scostella/Arduino-Light-Controller/Arduino Light Controller.kicad_sch

## KiCad design Arduino Light Controller.kicad_sch (2026-01-30)

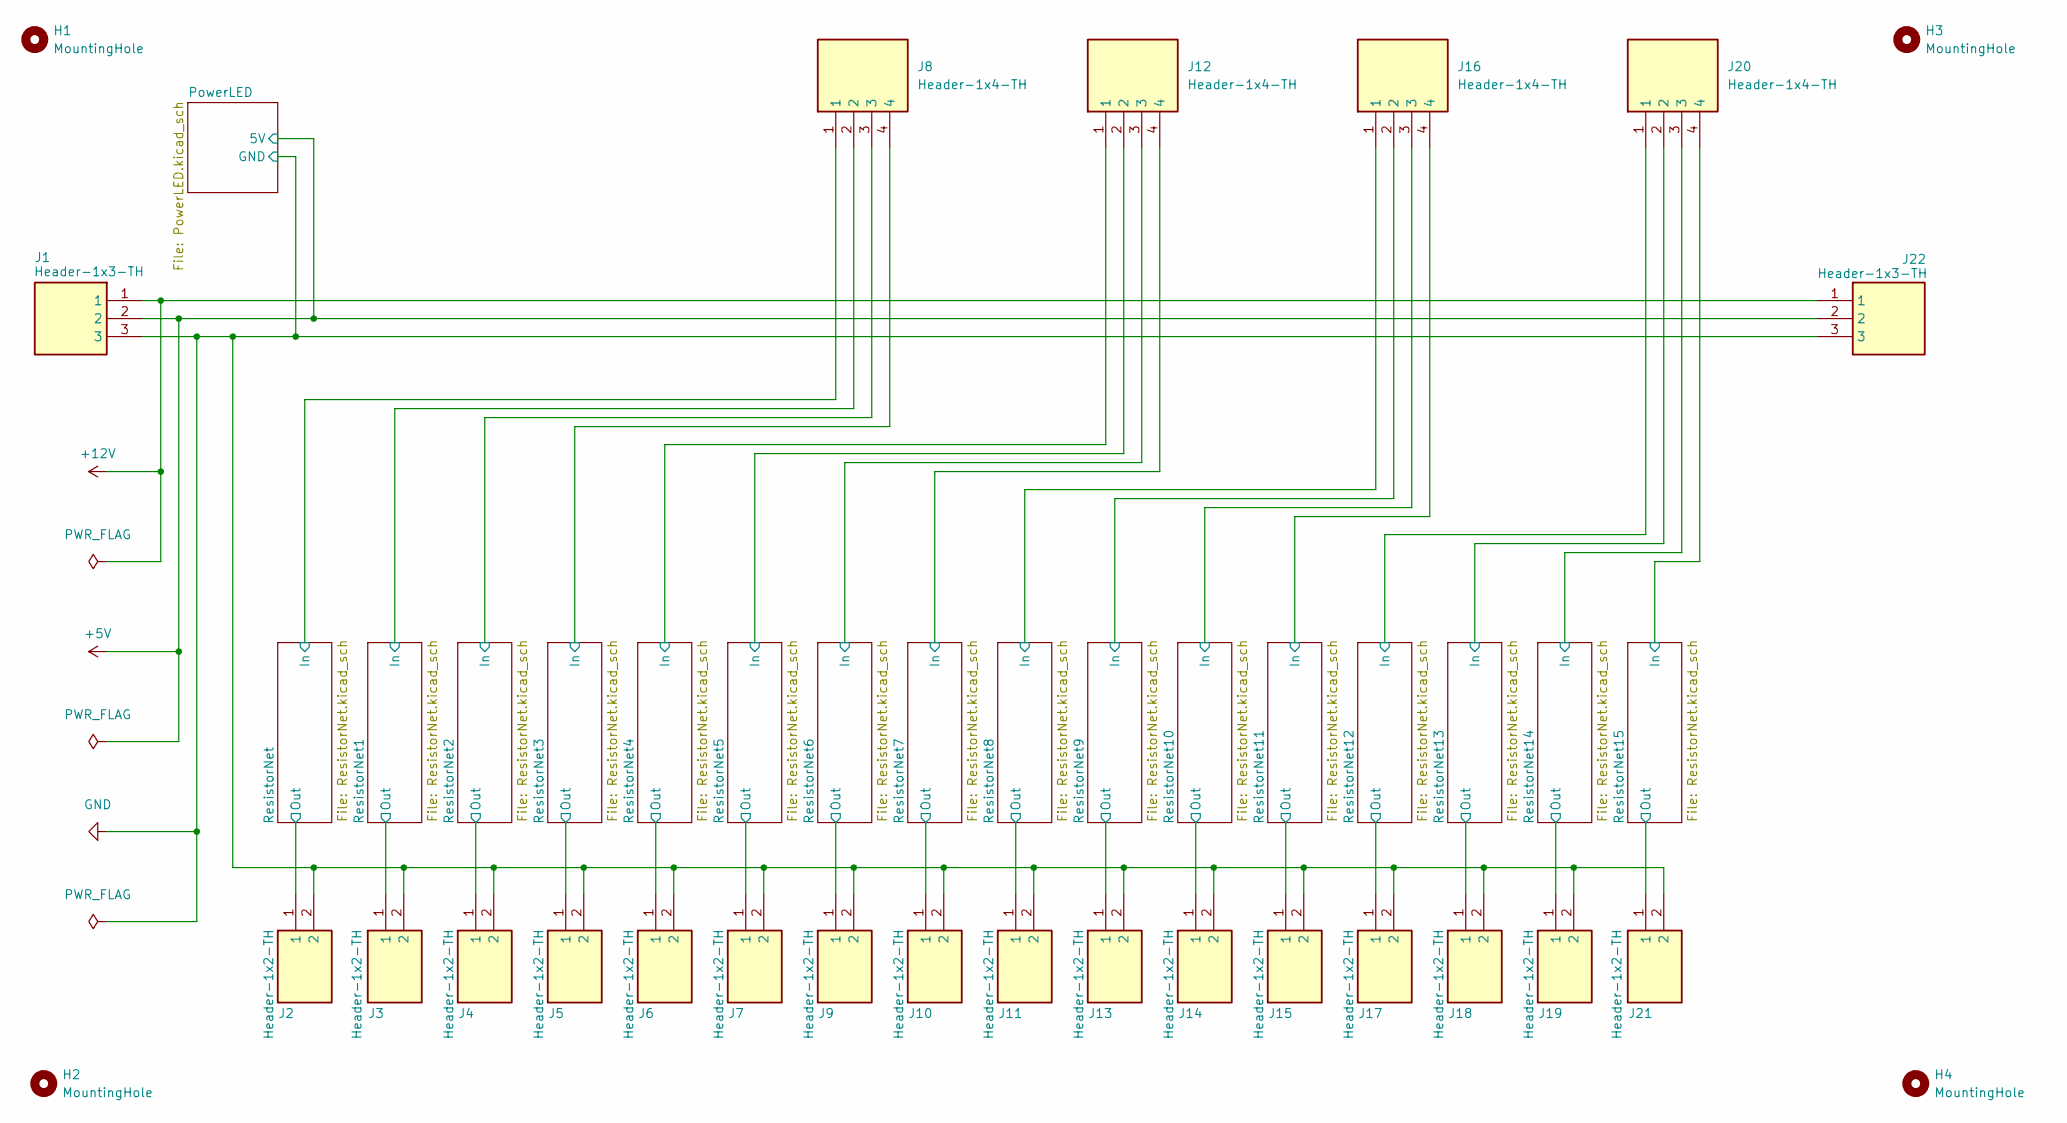
[picture p2: schematic Arduino Light Controller.kicad_sch]

Parts:
H1, H2, H3, H4: MountingHole; MountingHole_3.2mm_M3_ISO7380
J1, J22: Header-1x3-TH; 710-61300311121; Mouser Part Number 710-61300311121
J2, J3, J4, J5, J6, J7, J9, J10, J11, J13, J14, J15, J17, J18, J19, J21: Header-1x2-TH; 710-61300211121; Mouser Part Number 710-61300211121
J8, J12, J16, J20: Header-1x4-TH; 710-61300411121; Mouser Part Number 710-61300411121

Connections:
+5V: J1.2, J22.2
+12V: J1.1, J22.1
GND: J1.3, J2.2, J3.2, J4.2, J5.2, J6.2, J7.2, J9.2, J10.2, J11.2, J13.2, J14.2, J15.2, J17.2, J18.2, J19.2, J21.2, J22.3
In: J8.1, J8.2, J8.3, J8.4, J12.1, J12.2, J12.3, J12.4, J16.1, J16.2, J16.3, J16.4, J20.1, J20.2, J20.3, J20.4
Out: J2.1, J3.1, J4.1, J5.1, J6.1, J7.1, J9.1, J10.1, J11.1, J13.1, J14.1, J15.1, J17.1, J18.1, J19.1, J21.1
