scostella/Arduino-Light-Controller/PowerLED.kicad_sch

## KiCad design PowerLED.kicad_sch (2026-01-31)

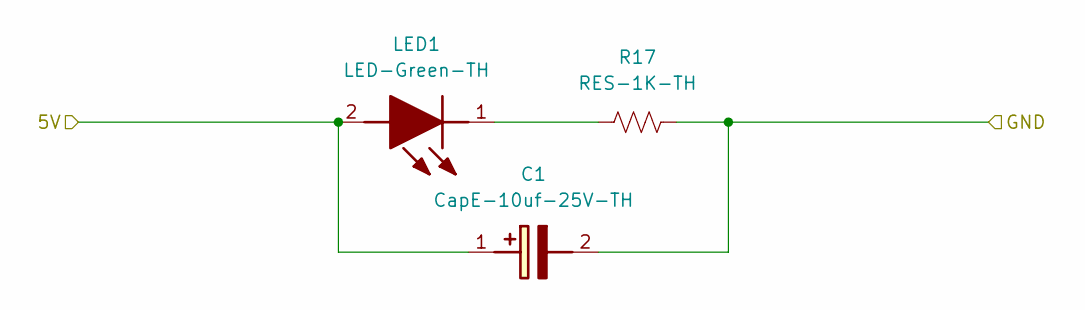
[picture p3: schematic PowerLED.kicad_sch]

Parts:
C1: CapE-10uf-25V-TH; 710-860010472002; Mouser Part Number 710-860010472002
LED1: LED-Green-TH; 604-WP7113GD; Mouser Part Number 604-WP7113GD
R17: RES-1K-TH; R_Axial_DIN0204_L3.6mm_D1.6mm_P7.62mm_Horizontal; Mouser Part Number N/A

Connections:
5V: C1.1 (+), LED1.2 (A)
GND: C1.2 (-), R17.2
unnamed: LED1.1 (K), R17.1
