scostella/Arduino-Light-Controller/ResistorNet.kicad_sch

## KiCad design ResistorNet.kicad_sch (2026-01-30)

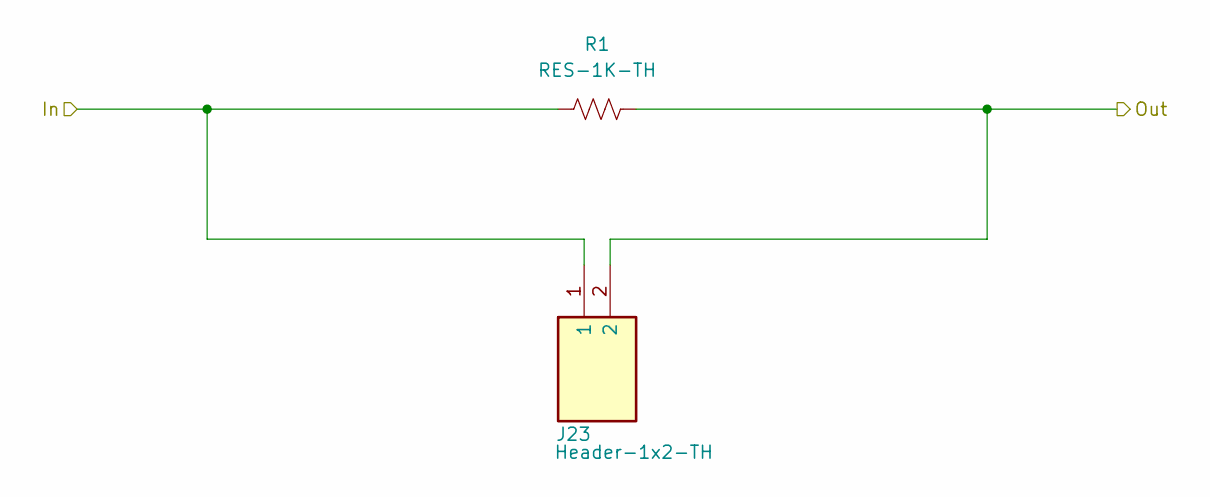
[picture p4: schematic ResistorNet.kicad_sch]

Parts:
J23: Header-1x2-TH; 710-61300211121; Mouser Part Number 710-61300211121
R1: RES-1K-TH; R_Axial_DIN0204_L3.6mm_D1.6mm_P7.62mm_Horizontal; Mouser Part Number N/A

Connections:
In: J23.1, R1.1
Out: J23.2, R1.2
